lv042/Weather-Wizard/images/html.png

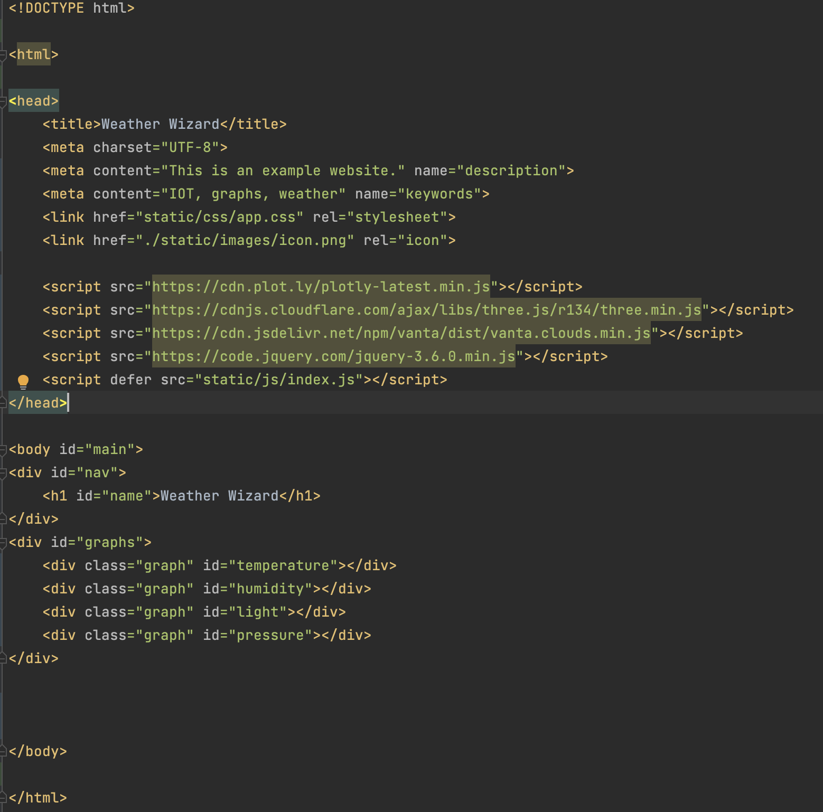
images/html.png
