lv042/Weather-Wizard/images/IMG20230310162710.jpg

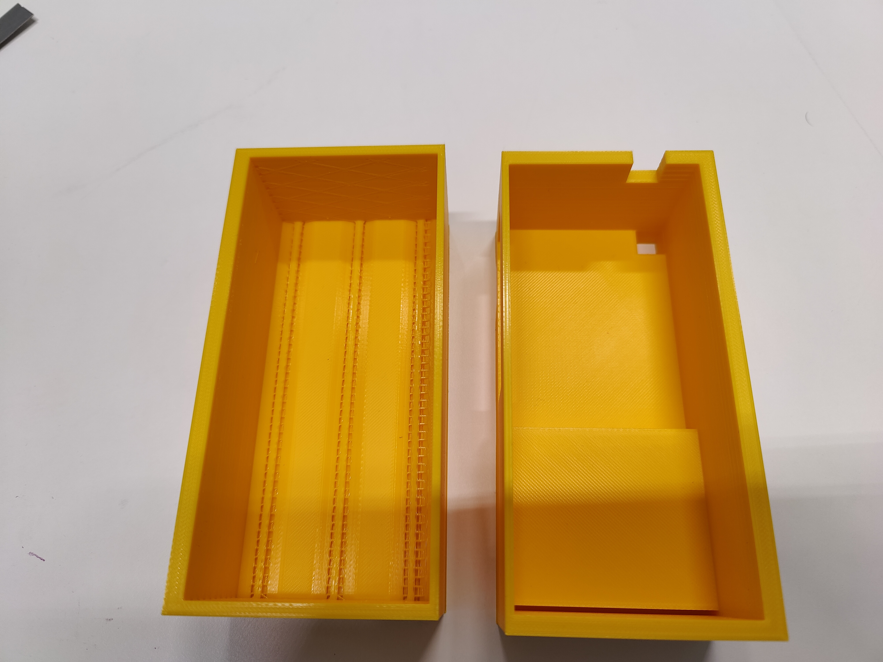
images/IMG20230310162710.jpg
