lv042/Weather-Wizard/images/IMG20230310163055.jpg

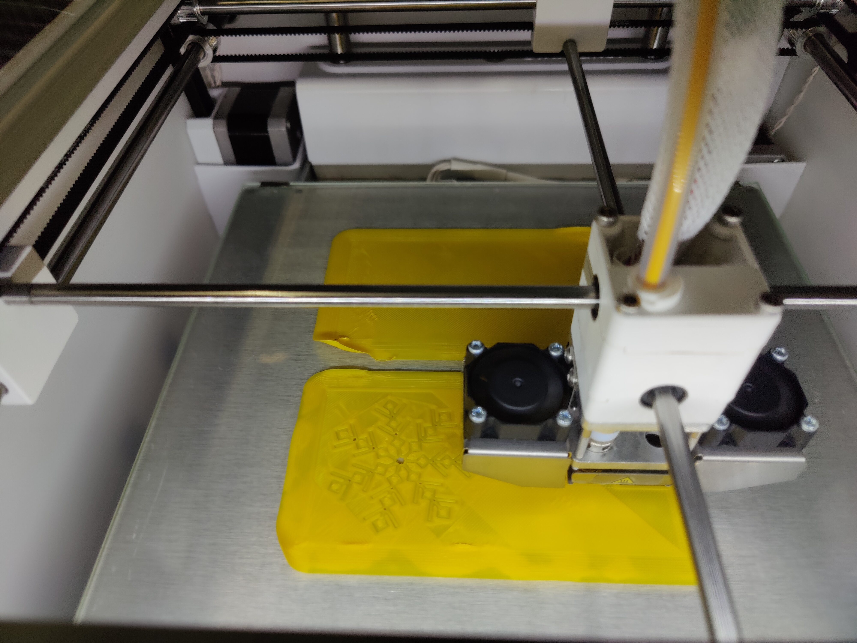
images/IMG20230310163055.jpg
