lv042/Weather-Wizard/images/IMG20230316124657.jpg

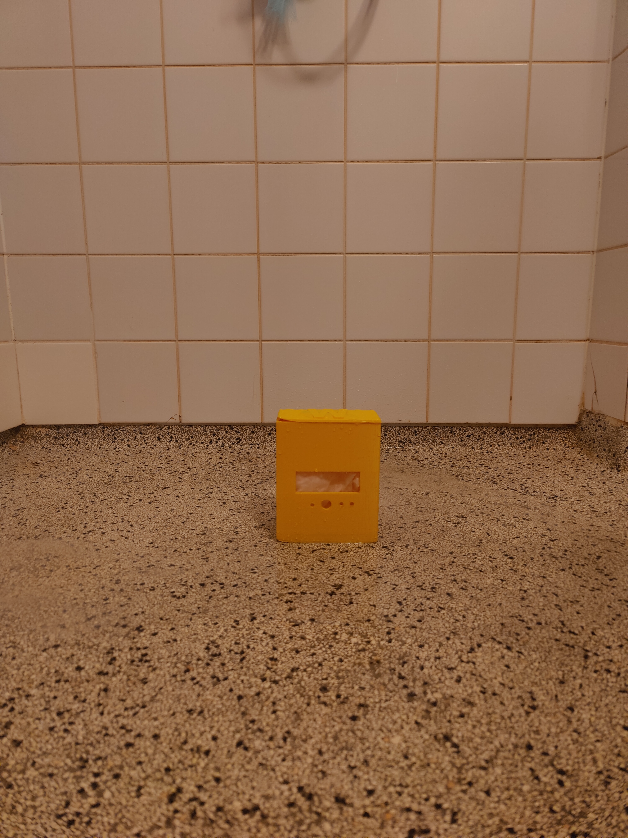
images/IMG20230316124657.jpg
