lv042/Weather-Wizard/images/IMG20230316124709.jpg

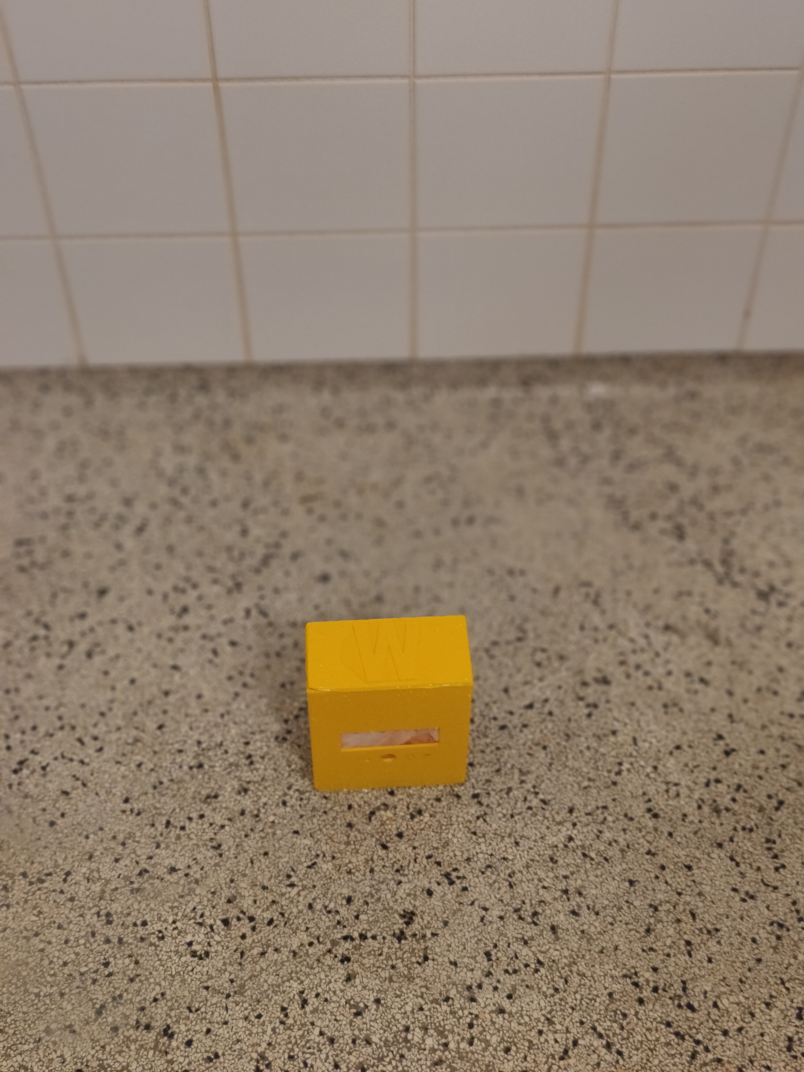
images/IMG20230316124709.jpg
