lv042/Weather-Wizard/images/IMG20230316125549.jpg

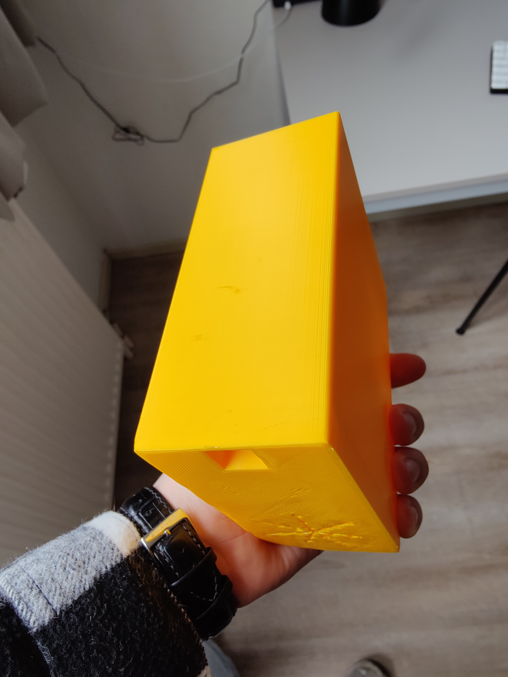
images/IMG20230316125549.jpg
